Kvenecusghost/Peggy/Software/Peggy_Tracker.X/EEPROM.png

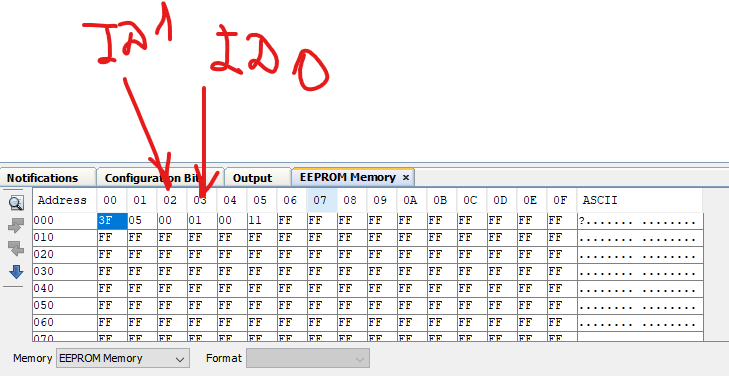
Software/Peggy_Tracker.X/EEPROM.png
