Kvenecusghost/Peggy/Software/Peggy_Tracker.X/Fuses AVRDUDESS Internal Oscillator.png

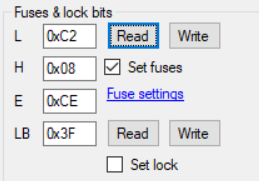
Software/Peggy_Tracker.X/Fuses AVRDUDESS Internal Oscillator.png
