Kvenecusghost/Peggy/Enclosure/Receiver/1910.step

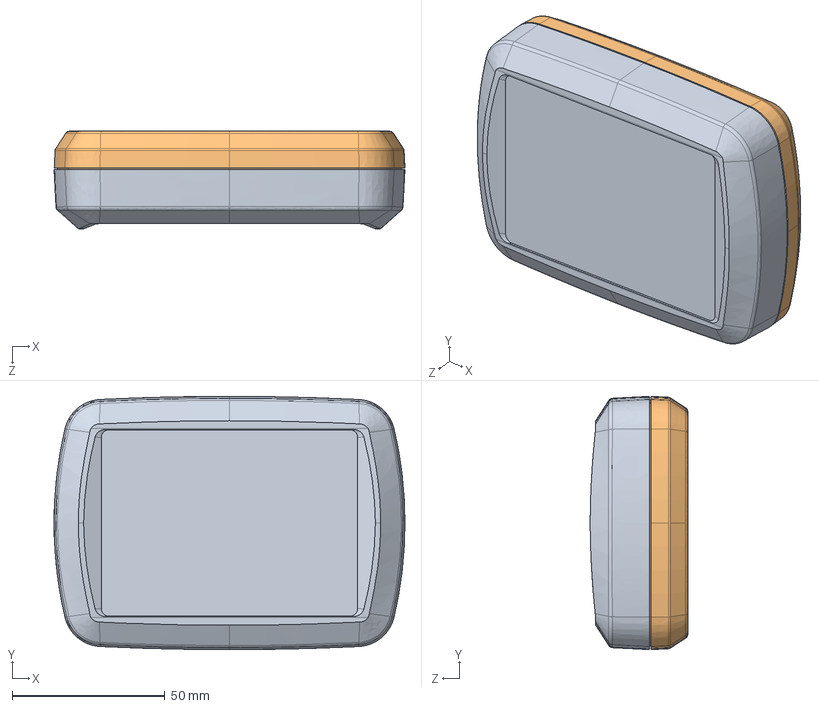
[picture p15: CAD file, 2022-12-06]
Enclosure/Receiver/1910.step
115.0 x 83.0 x 32.0 mm
