Kvenecusghost/Peggy/Hardware_fabrication/Tracker/v2.0 19.03.2022/3d/Case-08.SLDPRT

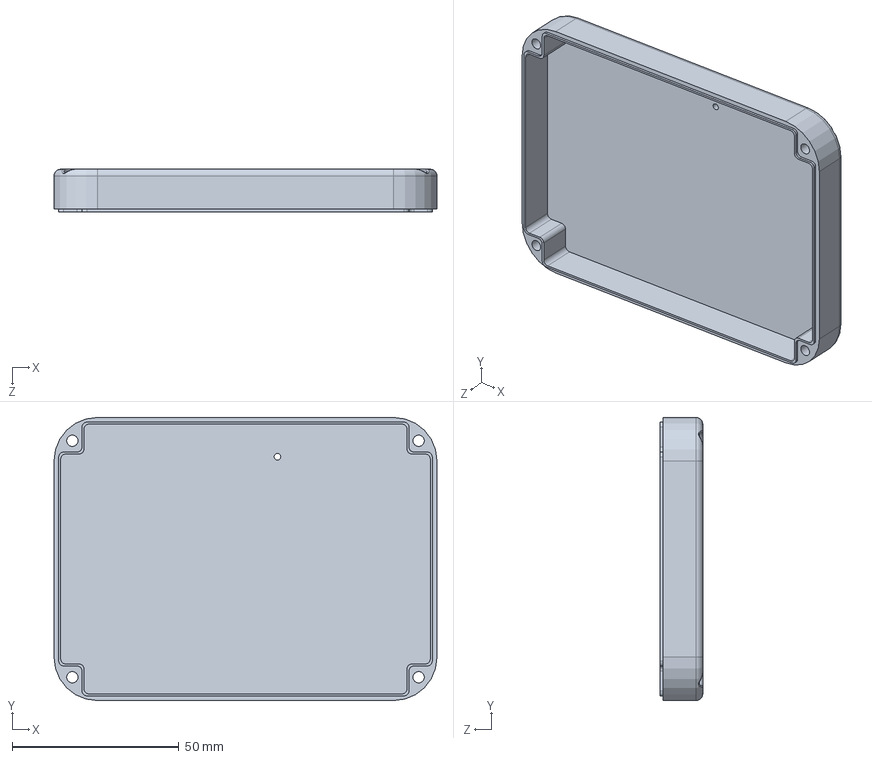
[picture p16: CAD file, 2022-10-07]
Hardware_fabrication/Tracker/v2.0 19.03.2022/3d/Case-08.SLDPRT
115.0 x 85.0 x 12.8 mm
