Kvenecusghost/Peggy/Enclosure/Receiver/G1910.SLDPRT

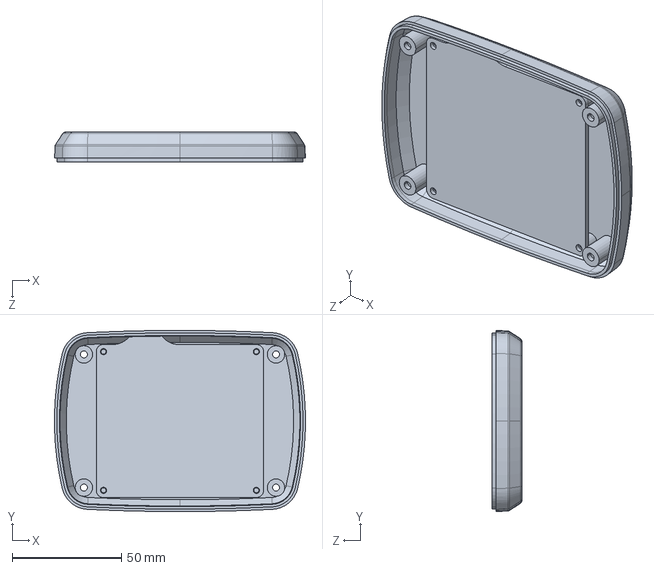
[picture p17: CAD file, 2022-12-06]
Enclosure/Receiver/G1910.SLDPRT
115.0 x 83.0 x 13.7 mm
