Kvenecusghost/Peggy/Hardware_fabrication/Tracker/v2.0 19.03.2022/3d/Ремень.SLDPRT

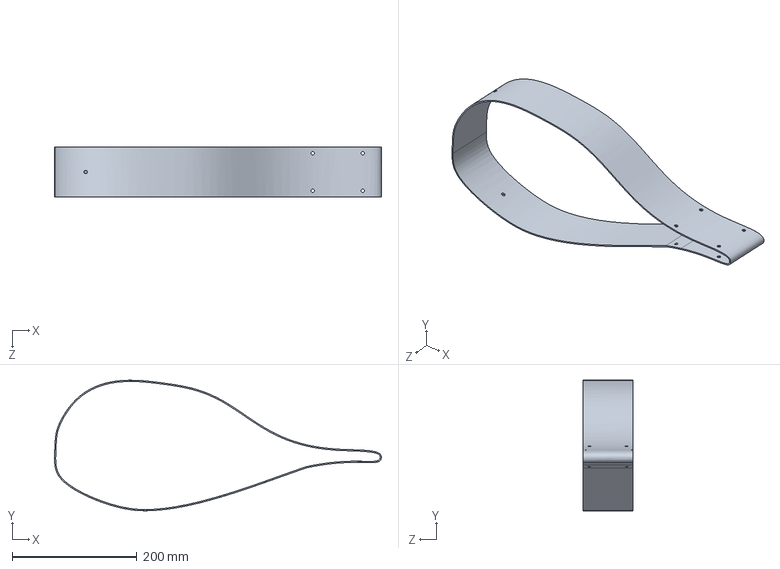
[picture p18: CAD file, 2022-10-07]
Hardware_fabrication/Tracker/v2.0 19.03.2022/3d/Ремень.SLDPRT
523.7 x 209.1 x 80.0 mm
