Kvenecusghost/Peggy/Hardware_fabrication/Tracker/v2.0 19.03.2022/3d/Металлическое крепление к ошейнику_1.SLDPRT

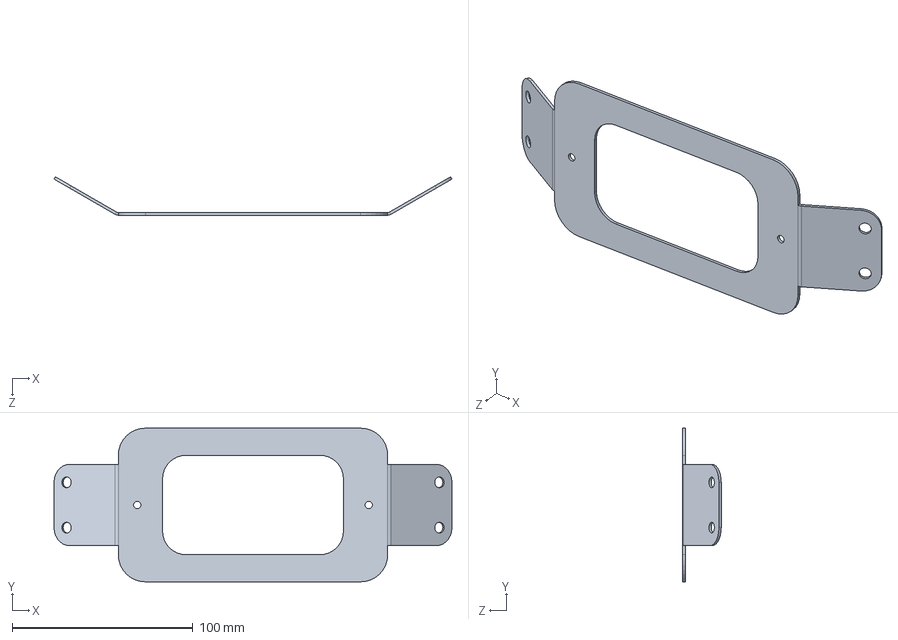
[picture p19: CAD file, 2022-10-07]
Hardware_fabrication/Tracker/v2.0 19.03.2022/3d/Металлическое крепление к ошейнику_1.SLDPRT
220.1 x 85.0 x 21.3 mm
