Kvenecusghost/Peggy/Hardware_fabrication/Tracker/v2.0 19.03.2022/3d/Case-07.SLDPRT

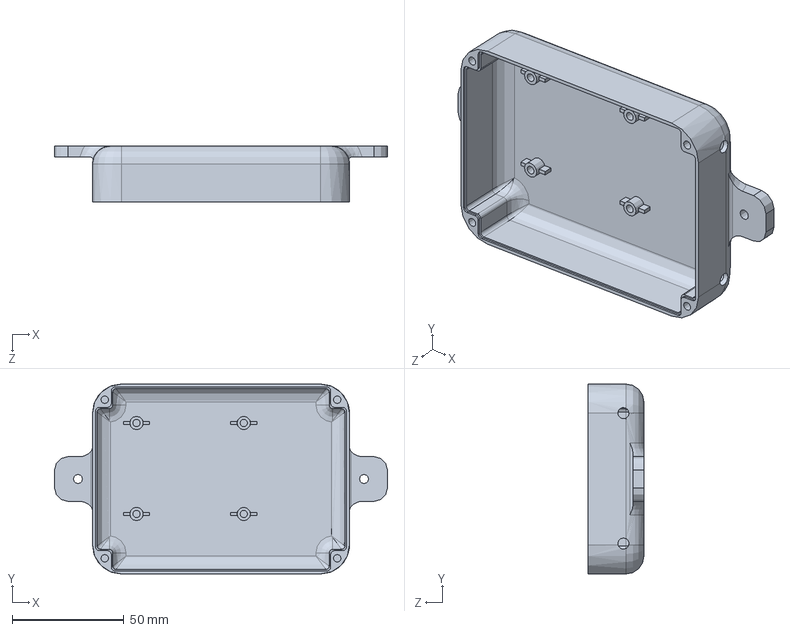
[picture p20: CAD file, 2022-10-07]
Hardware_fabrication/Tracker/v2.0 19.03.2022/3d/Case-07.SLDPRT
149.0 x 85.0 x 25.0 mm
