Kvenecusghost/Peggy/Hardware_fabrication/Tracker/v2.0 19.03.2022/3d/Case-05.SLDPRT

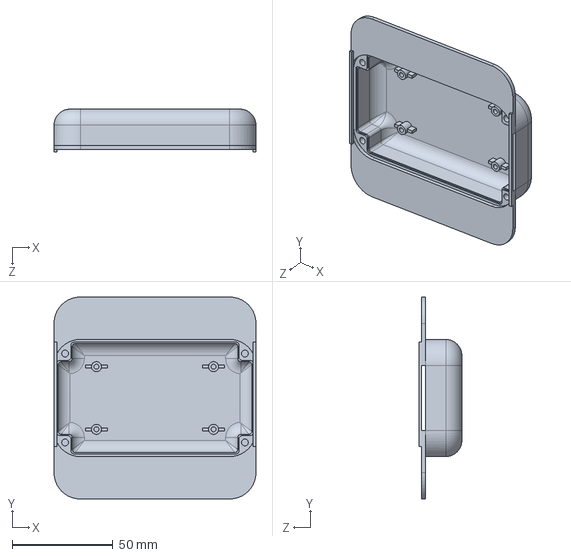
[picture p21: CAD file, 2022-08-23]
Hardware_fabrication/Tracker/v2.0 19.03.2022/3d/Case-05.SLDPRT
100.0 x 100.0 x 21.2 mm
