Kvenecusghost/Peggy/Hardware_fabrication/Tracker/v2.0 19.03.2022/3d/Металлическое крепление к ошейнику.SLDPRT

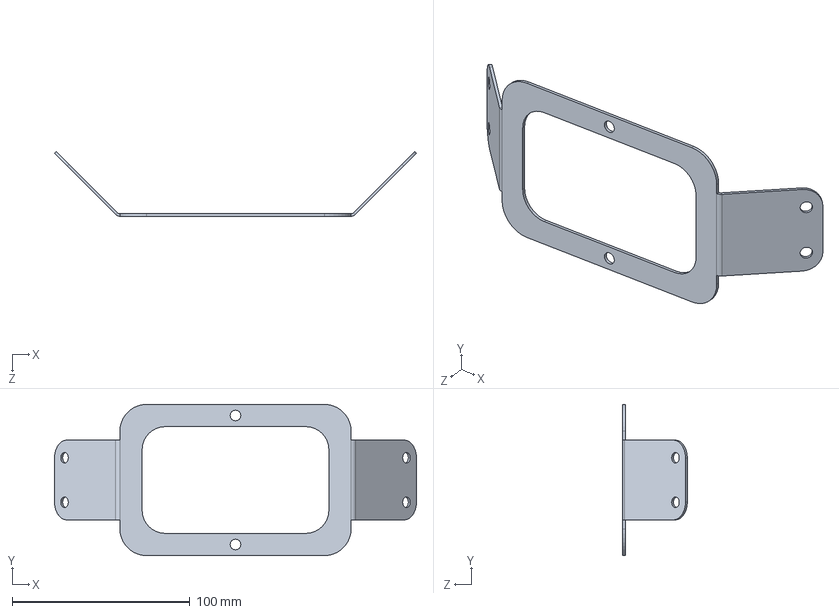
[picture p22: CAD file, 2022-08-23]
Hardware_fabrication/Tracker/v2.0 19.03.2022/3d/Металлическое крепление к ошейнику.SLDPRT
203.5 x 85.0 x 36.4 mm
