Kvenecusghost/Peggy/Hardware_fabrication/Tracker/v2.0 19.03.2022/3d/Батарейный отсек 2 18650.SLDPRT

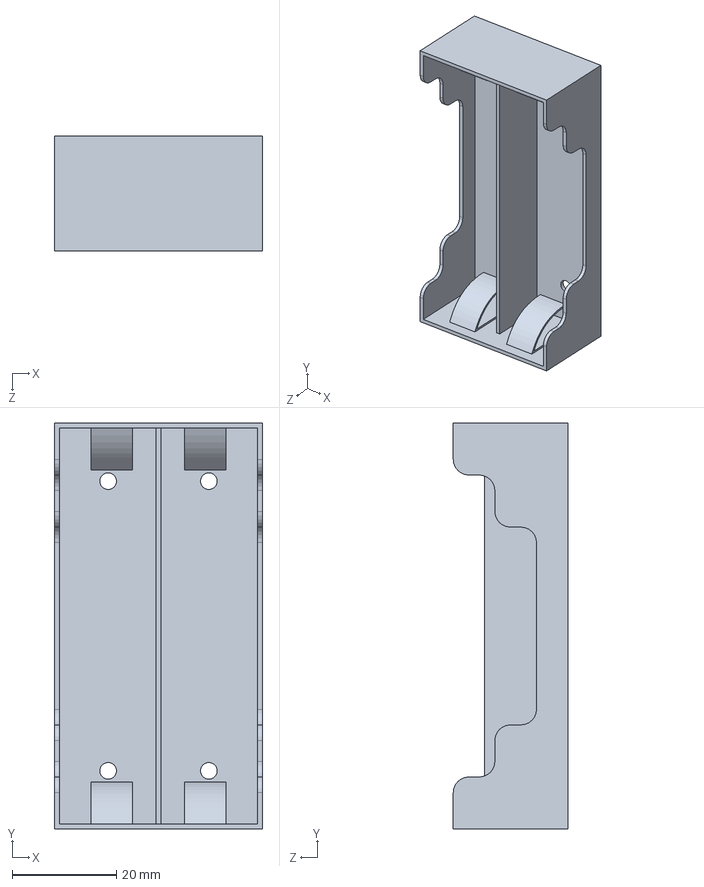
[picture p23: CAD file, 2022-08-23]
Hardware_fabrication/Tracker/v2.0 19.03.2022/3d/Батарейный отсек 2 18650.SLDPRT
40.0 x 78.0 x 22.0 mm
