Kvenecusghost/Peggy/Hardware_fabrication/Tracker/v2.0 19.03.2022/3d/Антенна MIKE3A.SLDPRT

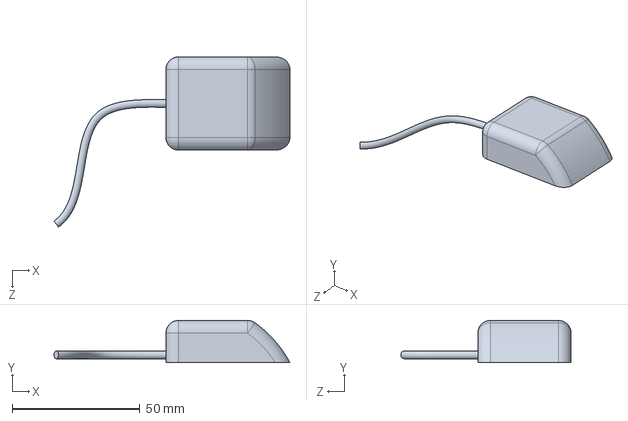
[picture p25: CAD file, 2022-08-04]
Hardware_fabrication/Tracker/v2.0 19.03.2022/3d/Антенна MIKE3A.SLDPRT
92.2 x 16.5 x 66.6 mm
