Kvenecusghost/Peggy/Hardware_fabrication/Tracker/v2.0 19.03.2022/3d/Антенна CRJKS0010-LNA-G65U.SLDPRT

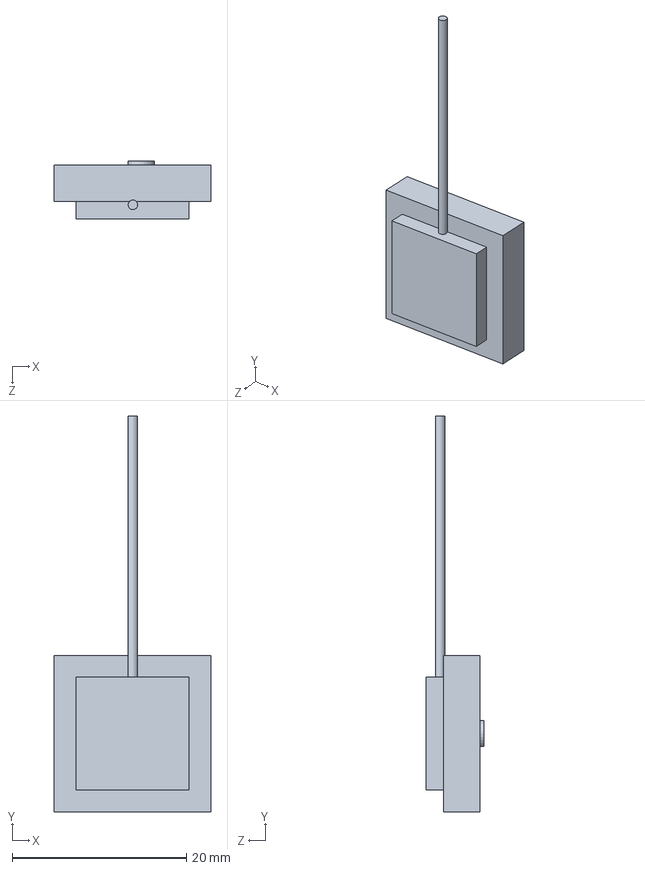
[picture p26: CAD file, 2022-08-04]
Hardware_fabrication/Tracker/v2.0 19.03.2022/3d/Антенна CRJKS0010-LNA-G65U.SLDPRT
18.0 x 45.5 x 6.70 mm
