Kvenecusghost/Peggy/Hardware_fabrication/Tracker/v2.0 19.03.2022/3d/Case-04.SLDPRT

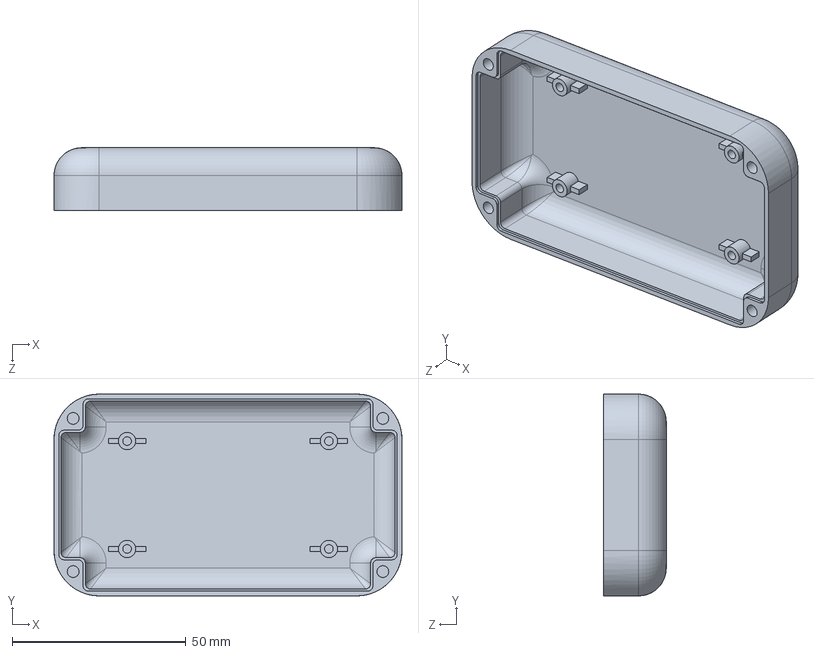
[picture p28: CAD file, 2022-06-09]
Hardware_fabrication/Tracker/v2.0 19.03.2022/3d/Case-04.SLDPRT
100.0 x 58.0 x 18.0 mm
