Kvenecusghost/Peggy/Hardware_fabrication/Tracker/v2.0 19.03.2022/3d/Case-02.SLDPRT

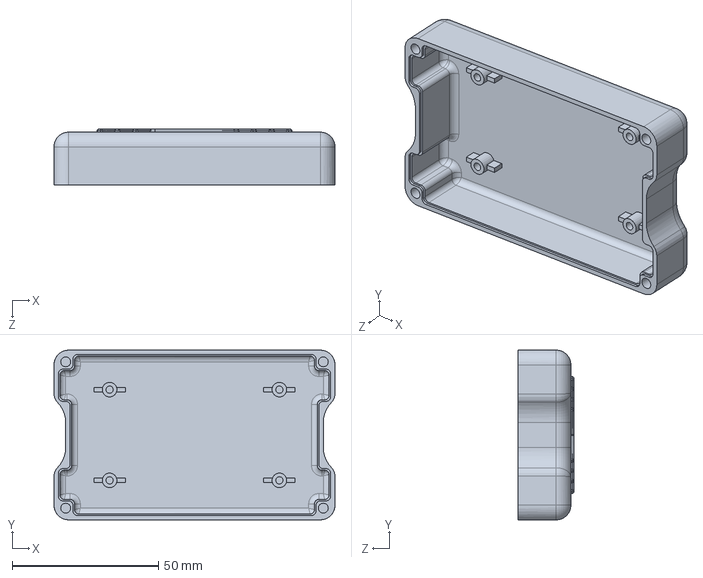
[picture p29: CAD file, 2022-06-09]
Hardware_fabrication/Tracker/v2.0 19.03.2022/3d/Case-02.SLDPRT
96.0 x 58.0 x 19.0 mm
