Kvenecusghost/Peggy/Hardware_fabrication/Tracker/v2.0 19.03.2022/3d/Case-01.SLDPRT

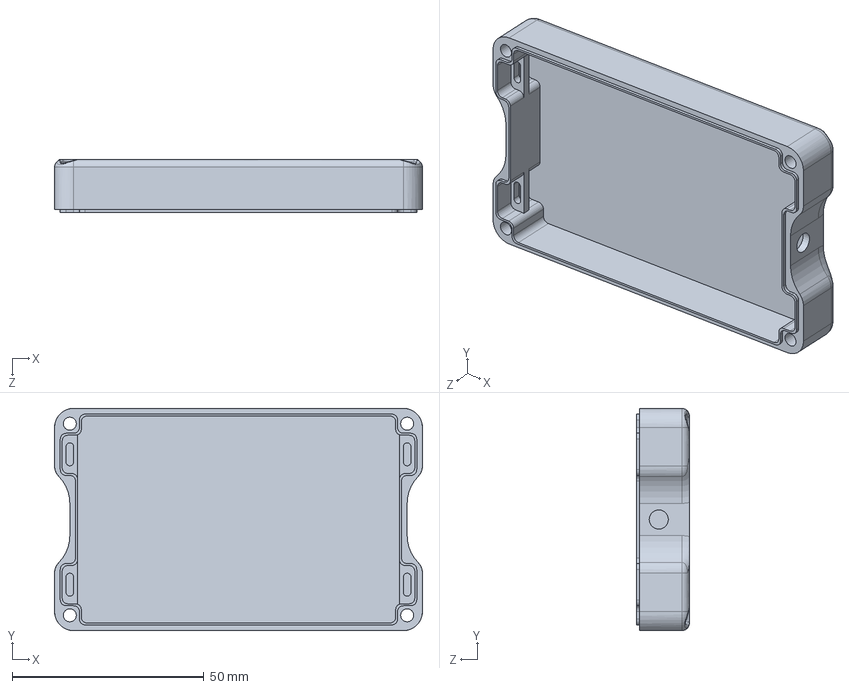
[picture p30: CAD file, 2022-06-09]
Hardware_fabrication/Tracker/v2.0 19.03.2022/3d/Case-01.SLDPRT
96.0 x 58.0 x 13.8 mm
