Kvenecusghost/Peggy/Hardware_fabrication/Tracker/v2.0 19.03.2022/3d/Belt mate 2.SLDPRT

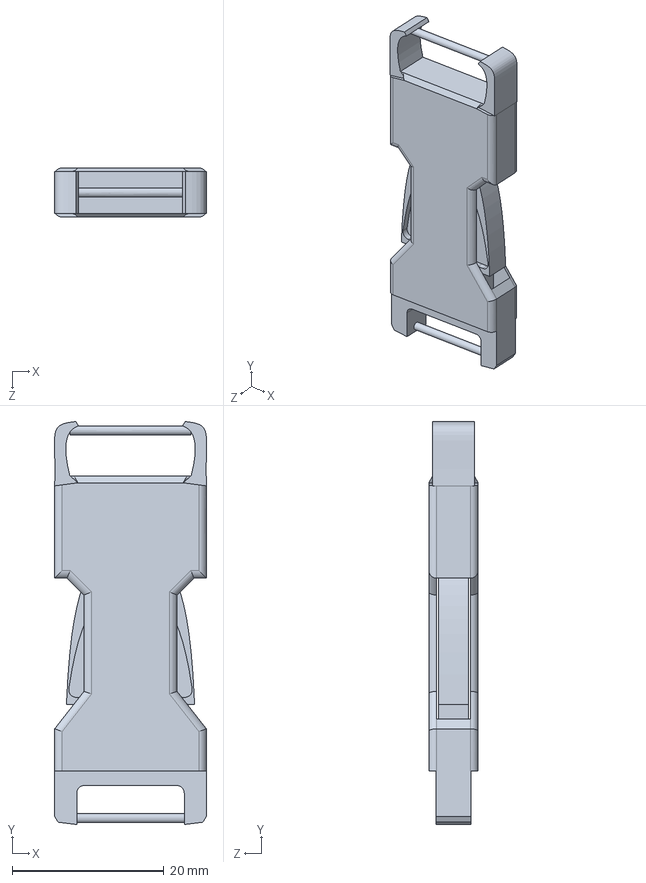
[picture p31: CAD file, 2022-06-06]
Hardware_fabrication/Tracker/v2.0 19.03.2022/3d/Belt mate 2.SLDPRT
20.0 x 53.1 x 6.50 mm
