Kvenecusghost/Peggy/Hardware_fabrication/Tracker/v2.0 19.03.2022/3d/Аккумулятор литий-полимерный LP115181.SLDPRT

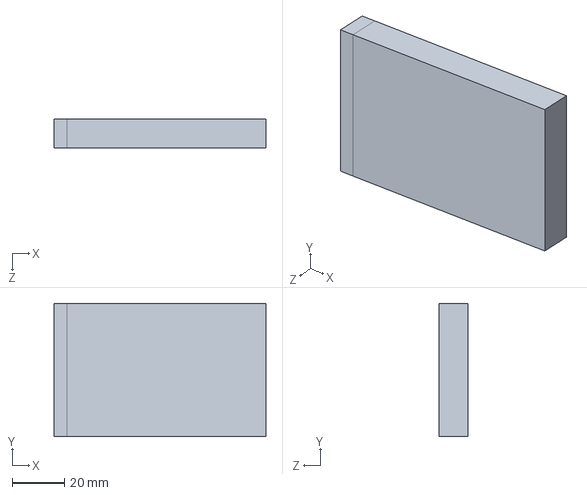
[picture p32: CAD file, 2022-06-06]
Hardware_fabrication/Tracker/v2.0 19.03.2022/3d/Аккумулятор литий-полимерный LP115181.SLDPRT
81.0 x 51.0 x 11.0 mm
