Kvenecusghost/Peggy/Hardware_fabrication/Tracker/v2.0 19.03.2022/3d/Belt 3.SLDPRT

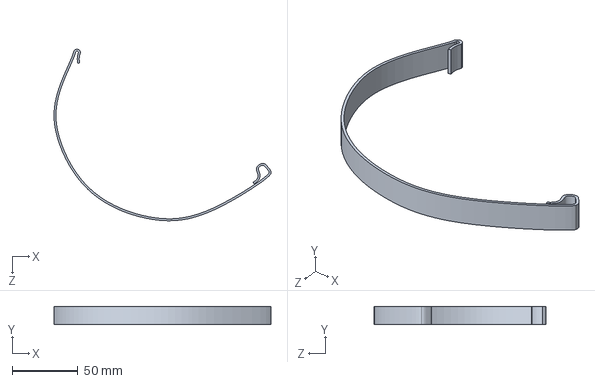
[picture p33: CAD file, 2022-06-06]
Hardware_fabrication/Tracker/v2.0 19.03.2022/3d/Belt 3.SLDPRT
165.2 x 14.0 x 130.6 mm
