Kvenecusghost/Peggy/Hardware_fabrication/Tracker/v2.0 19.03.2022/3d/Печатная плата Peggy Tracker.step

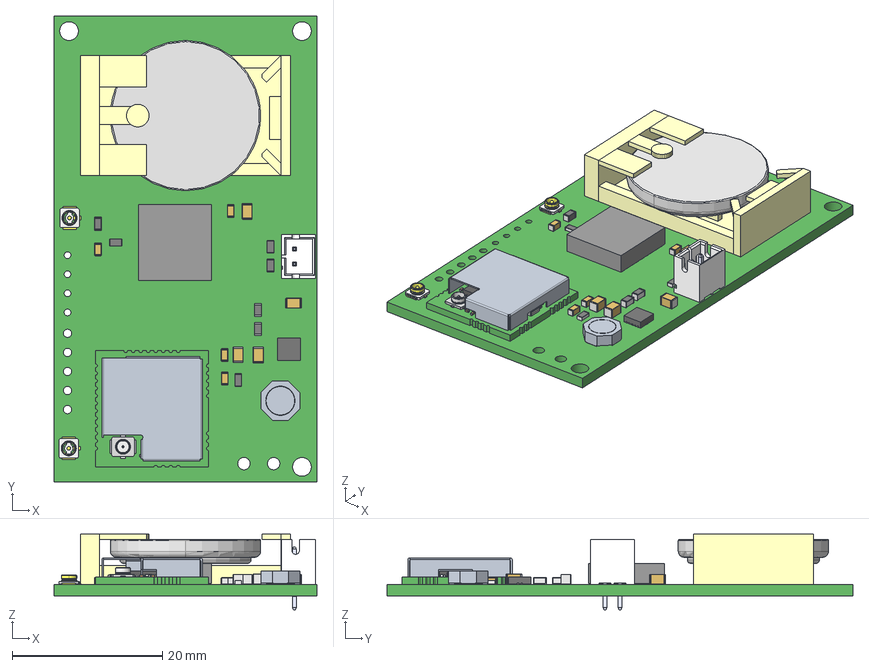
[picture p34: CAD file, 2022-03-18]
Hardware_fabrication/Tracker/v2.0 19.03.2022/3d/Печатная плата Peggy Tracker.step
35.0 x 62.0 x 10.1 mm
CircuitWorks-BATT_CR2032
Extruded x 15
IPX x 2
Mid_Body x 6
Open_CASCADE_STEP_translator_6.8_15.2.1 x 8
Mark x 6
B2B-PH-K-S(LF)(SN)--3DModel-STEP-56544
Open_CASCADE_STEP_translator_6.8_12.2.1 x 4
Open_CASCADE_STEP_translator_6.8_2.1.1
Open_CASCADE_STEP_translator_6.8_2.1.2
Open_CASCADE_STEP_translator_6.8_2.2.1
Open_CASCADE_STEP_translator_6.8_1.1.1.1
0201_SMD_Capacitor x 36
R0201 x 7
RES_1005-0402 x 3
QFN48_7x7
NT2016SA
C0402 x 4
crystal_rtf2012
D030A-そ敖裔
Pins
BODY-SON
Open_CASCADE_STEP_translator_6.8_5.1.1 x 5
Open_CASCADE_STEP_translator_6.8_5.1.2 x 5
Open_CASCADE_STEP_translator_6.8_5.2.1 x 5
Open_CASCADE_STEP_translator_6.8_24.1.1 x 3
Open_CASCADE_STEP_translator_6.8_24.1.2 x 3
Open_CASCADE_STEP_translator_6.8_24.2.1 x 3
