Kvenecusghost/Peggy/Software/Peggy_Tracker.X/main.h

/* 
 * @file main.h
 * @author Jedi
 * @date 27 декабря 2021 г., 19:02
 */

#ifndef MAIN_H
#define	MAIN_H

#ifdef	__cplusplus
extern "C" {
#endif

#include <xc.h>

#ifdef	__cplusplus
}
#endif

#endif	/* MAIN_H */
